BombilCalabasov/3DPrint_BodyCase4PRIandDraginoLoRaHATwithScreen/IMAG1935.jpg

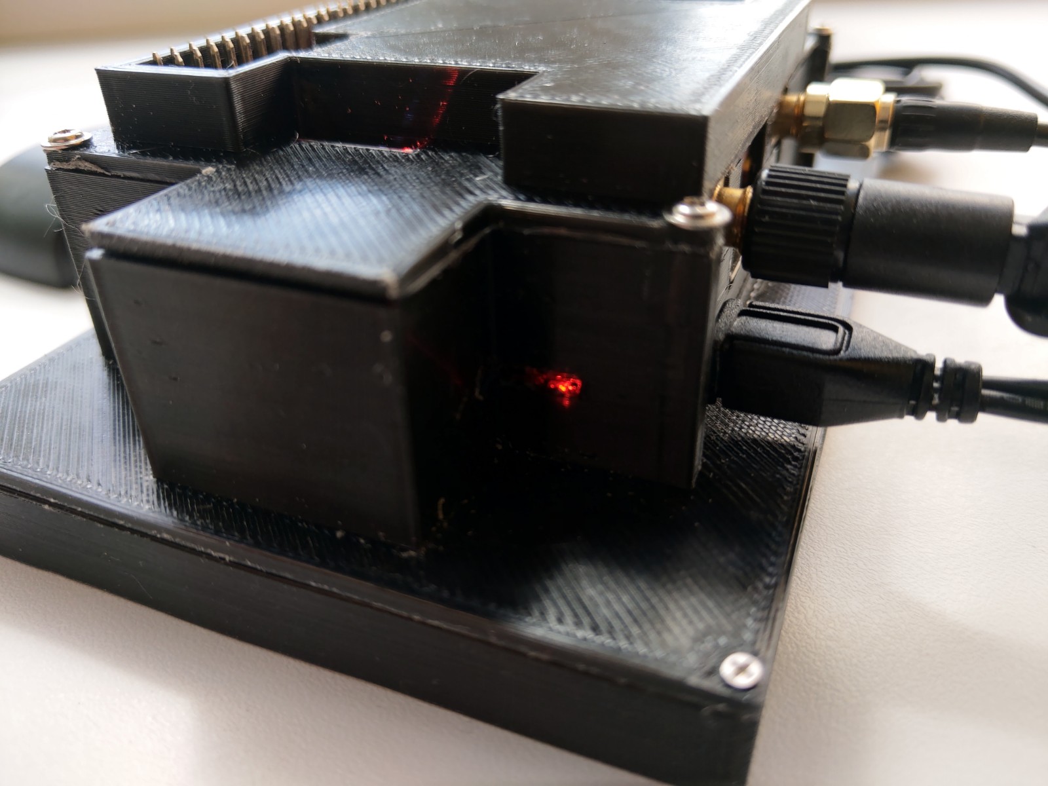
IMAG1935.jpg
